Tinkerforge/analog-out-v2-bricklet/software/src/config.h

/* analog-out-v2-bricklet
 * Copyright (C) 2015 Olaf Lüke <olaf@tinkerforge.com>
 *
 * config.h: Analog Out Bricklet 2.0 specific configuration
 *
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
 * You should have received a copy of the GNU Lesser General Public
 * License along with this library; if not, write to the
 * Free Software Foundation, Inc., 59 Temple Place - Suite 330,
 * Boston, MA 02111-1307, USA.
 */

#ifndef CONFIG_H
#define CONFIG_H

#include <stdint.h>
#include <stdbool.h>

#include "bricklib/drivers/board/sam3s/SAM3S.h"

#include "analog-out.h"

#define BRICKLET_FIRMWARE_VERSION_MAJOR 2
#define BRICKLET_FIRMWARE_VERSION_MINOR 0
#define BRICKLET_FIRMWARE_VERSION_REVISION 0

#define BRICKLET_HARDWARE_VERSION_MAJOR 2
#define BRICKLET_HARDWARE_VERSION_MINOR 0
#define BRICKLET_HARDWARE_VERSION_REVISION 0

#define BRICKLET_DEVICE_IDENTIFIER 256

#define MAX_ADC_VALUE ((1  << 12) - 1)
#define MAX_VOLTAGE 3300

#define LOGGING_LEVEL LOGGING_DEBUG
#define DEBUG_BRICKLET 0

#define INVOCATION_IN_BRICKLET_CODE

#define PIN_REF_VOLTAGE (BS->pin1_ad)

typedef struct {
	uint32_t last_input_voltage_sum;
	uint32_t input_voltage_sum;
	uint8_t counter;

	uint16_t last_output_voltage;
} BrickContext;

#endif
